kquinsland/modular-rack-mount-power-system/site/content/system/hardware/gateway/_files/gateway-concept.prompt.txt

Generator: built-in image_gen tool
Asset: gateway-concept.webp (converted from the generated PNG with cwebp, quality 88)

Final prompt:
Use case: stylized-concept.
Asset type: concept placeholder illustration for a technical documentation page about a modular rack power gateway.
Primary request: a restrained, polished 3D concept render of one small ESP32-based wireless-to-CAN-FD gateway board for telemetry and remote control.
Subject: compact rectangular green PCB, a shielded ESP32-style wireless module with a visible printed antenna at the board edge, two small black interface ICs, a modest cluster of passive components, a single four-position pluggable screw terminal for the power/CAN connection, four corner mounting holes. Sparse, plausible arrangement; the image is illustrative, not a production board layout.
Scene/backdrop: plain neutral charcoal-gray studio background, subtle grounding shadow, no surrounding props.
Composition/framing: landscape 3:2 image, elevated three-quarter perspective, entire board visible and centered with generous clean margins, crisp enough for a documentation figure.
Style/medium: understated industrial CAD-style product visualization, matte green solder mask, brushed-metal RF shield, realistic connectors, soft diffuse lighting. No exaggerated glow or science-fiction styling.
Constraints: no text, labels, logos, watermark, dimensions, cables, rack enclosure, display, or extra boards. No reference images.
