kquinsland/modular-rack-mount-power-system/docs/interfaces.md

# Consolidated Backplane Interfaces

This document describes the active second-generation backplane hardware in
`hardware/boards/backplane`. The controller and all six slots live on one PCB.

## DC Input

Backplane `J8` uses DORABO `DB910-6.35-2P-GN-S`, LCSC `C395872`, and is
intentionally DNP for manual installation.

| Pin | Signal | Direction | Notes |
| ---: | --- | --- | --- |
| 1 | `GND` | Input | Common power and signal return. |
| 2 | `VIN_RAW` | Input | Nominal 24 V for the first population. |

`VIN_RAW` passes through the 1 mOhm high-side shunt `RSH1` to `VIN_BUS`. The
INA237 measures this drop through 10 ohm/100 nF input filtering; its PCB sense
connections must be Kelvin-routed directly to the shunt pads.

## External CAN-FD

Backplane `J7` uses the XINLAIYA XY308-2.54-3P footprint, LCSC `C557686`, and
is intentionally DNP for manual installation.

| Pin | Signal | Direction | Notes |
| ---: | --- | --- | --- |
| 1 | `GND` | Shared | CAN reference/return. |
| 2 | `CAN_EXT_N` | Bidirectional | External CAN low (`CANL`). |
| 3 | `CAN_EXT_P` | Bidirectional | External CAN high (`CANH`). |

`D1` provides connector-side CAN ESD protection and `L3` is the boundary common-
mode choke. `SJ1` enables `R17`, the normally-open 120 ohm termination, only
when the backplane is installed at a physical end of the CAN bus.

Both sides of `L3` use KiCad's paired-net naming convention: `P` is `CANH` and
`N` is `CANL`. The PCB rules require 0.20-0.30 mm pair gap (0.25 mm preferred),
no more than 5 mm uncoupled length, and no more than 1 mm within-pair skew.

The TCAN3413 standby input is tied low, so the transceiver is permanently
active whenever 3.3 V is present. MCU-controlled standby is not required.

## Carrier Slots

The six carrier slots use the carrier-authoritative AMASS
`XT30U(2+2)-F.G.B`, LCSC `C30170181`, footprint and pinout.

| Slot | Reference |
| ---: | --- |
| 1 | `J1` |
| 2 | `J2` |
| 3 | `J3` |
| 4 | `J4` |
| 5 | `J5` |
| 6 | `J6` |

| Physical pin | Signal | Direction | Notes |
| ---: | --- | --- | --- |
| 1 | `VIN_BUS` | Backplane to carrier | Unswitched high-current slot supply. |
| 2 | `GND` | Shared | Power and CAN return. |
| 3 | `CAN_BUS_P` | Bidirectional | Shared CAN-FD high (`CANH`). |
| 4 | `CAN_BUS_N` | Bidirectional | Shared CAN-FD low (`CANL`). |

There is no per-slot backplane ESD network. The backplane protects its external
CAN connector, and each carrier retains its own connector-side CAN protection.
The PCB layout must implement a short shared CAN trunk with short slot stubs.

## Local I2C

`I2C_SDA` and `I2C_SCL` use STM32 PA6 and PA7 respectively on I2C2 and connect
only the STM32C092GCU6 and INA237 on the backplane. They use 2.2 kohm pull-ups
to 3.3 V. No I2C signal reaches a carrier slot.

## Fans

`J9` and `J11` use KiCad's vertical 2.54 mm 3-wire fan-header footprint. The
exact purchasable header MPN is not yet selected and must be checked against
that footprint before quoting. Each connector has an independent high-side
supply-PWM switch and tach input.

| Pin | `J9` signal | `J11` signal | Notes |
| ---: | --- | --- | --- |
| 1 | `GND` | `GND` | Fan return. |
| 2 | `FAN_12V_SW` | `FAN2_12V_SW` | Independently switched 12 V from Q1 or Q3. |
| 3 | `FAN_TACH` | `FAN2_TACH` | Open-collector tach input with a 10 kohm pull-up to 3.3 V. |

The interfaces support 3-wire fans only. They do not provide the fourth control
wire used by 4-wire PWM fans. Both connectors share the 1 A LM5164 12 V rail;
combined continuous current, simultaneous startup, and stall behavior require
first-article validation.

Fan 0 uses STM32 PA2 for supply PWM and PB8 for tach capture. Fan 1 uses PA0
for supply PWM and PA8 for tach capture.

## External Temperature Sensor

`J12` is a standard vertical 2.54 mm 1x3 header for an externally powered
DS18B20:

| Pin | Signal | Notes |
| ---: | --- | --- |
| 1 | `GND` | Sensor return. |
| 2 | `DS18B20_DATA` | 1-Wire DQ to STM32 PA15. |
| 3 | `+3V3` | External sensor supply. |

`R24` is a 4.7 kohm pull-up from DQ to 3.3 V. This is the three-wire external-
supply arrangement; no parasite-power strong-pull-up circuit is provided. Any
cable-end bypass capacitor should be placed next to the sensor.

The backplane status NeoPixel (`LED1`) is driven from STM32 `PA1` through a
100 ohm series resistor and has a dedicated 100 nF local bypass capacitor.

## SWD

`J10` is a Tag-Connect `TC2030-IDC-NL` footprint with this schematic pinout:

| Pin | Signal |
| ---: | --- |
| 1 | `+3V3` target reference |
| 2 | `SWDIO` |
| 3 | `NRST` |
| 4 | `SWCLK` |
| 5 | `GND` |
| 6 | Not connected |

## Local Power Rails

Separate LM5164DDAR converters generate 3.3 V and 12 V from `VIN_BUS`. Both
use PSPMAA0805-101M-ANP 100 uH inductors, but their feedback, RON,
ripple-injection, and output-capacitor networks are rail-specific.
