kquinsland/modular-rack-mount-power-system/hardware/artwork/indy/indy-size-proof.pdf

## Indy: actual-size silkscreen comparison

Print at 100% / Actual Size. Do not fit to page.
White = silk ink; green = board. Screen size is not calibrated.
50 mm tall x 40.2 mm wide | 75 mm tall x 60.3 mm wide

100 mm tall x 80.4 mm wide

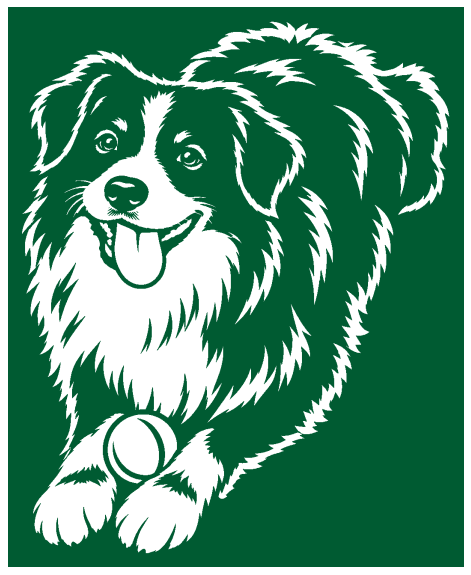
[picture p8: figure]

75 mm: preferred starting size 100 mm: more fine detail
50 mm: fine lines may drop out

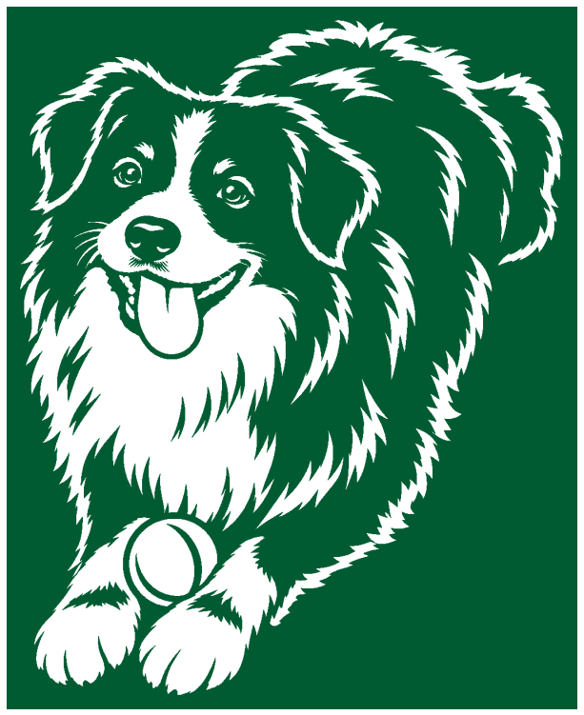
[picture p9: figure]

Artwork is a faithful trace, not a fabrication simulation. Whiskers, eye details and fur tips still need fabrication review.

This bar must measure 50 mm on paper.
