kquinsland/modular-rack-mount-power-system/site/content/system/_files/backplane-power-cap.webp

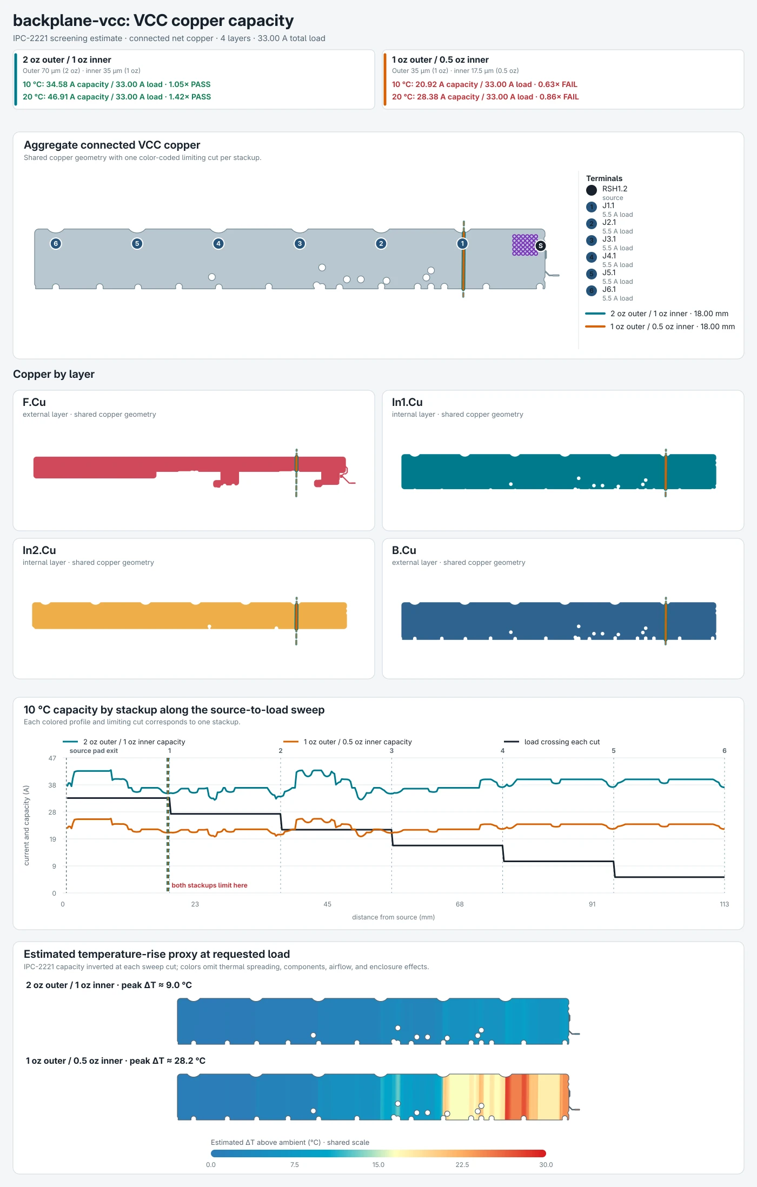
site/content/system/_files/backplane-power-cap.webp
