kquinsland/modular-rack-mount-power-system/site/content/_files/hardware-assemblies.webp

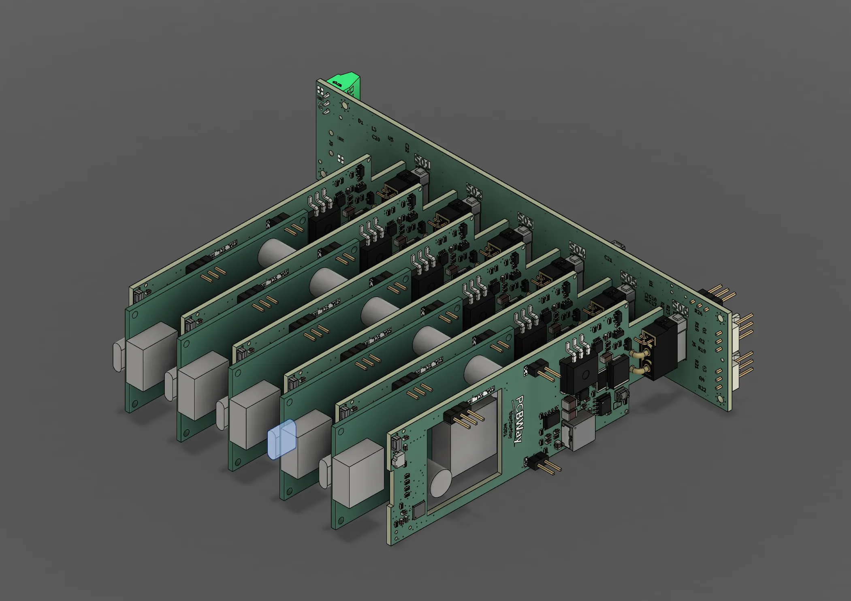
site/content/_files/hardware-assemblies.webp
