kquinsland/modular-rack-mount-power-system/site/content/worklogs/2026/09/10 - First Physical Prototypes/_files/early_prototype_01.webp

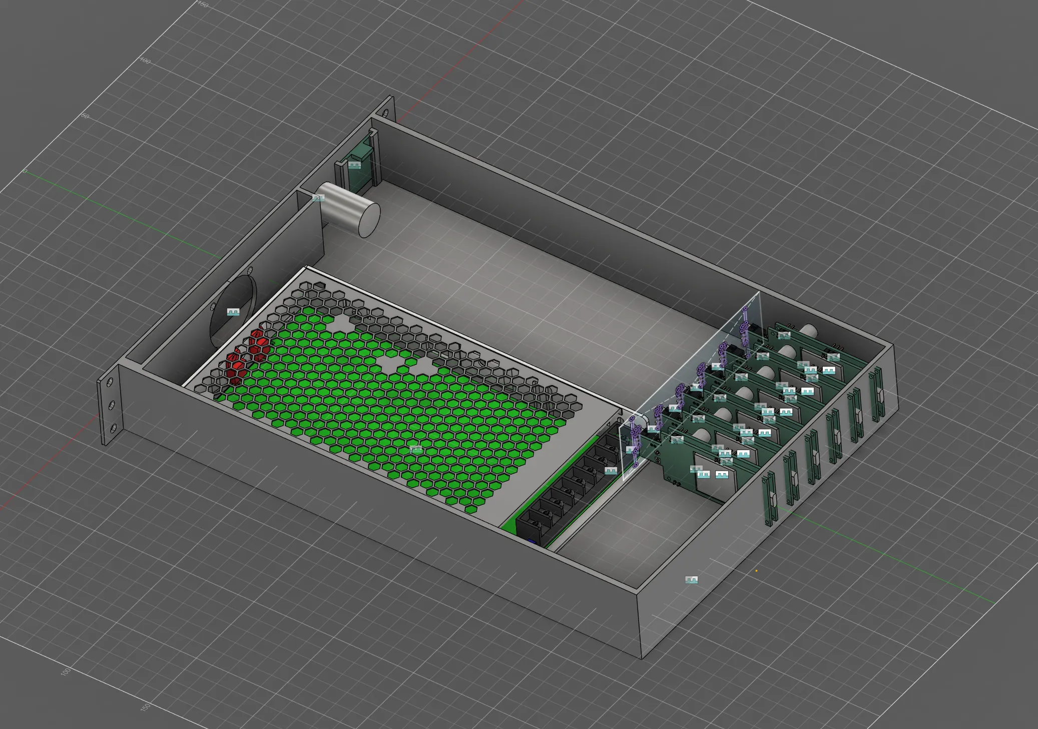
site/content/worklogs/2026/09/10 - First Physical Prototypes/_files/early_prototype_01.webp
